lizardbeans/sdvxminicon/img/024.jpg

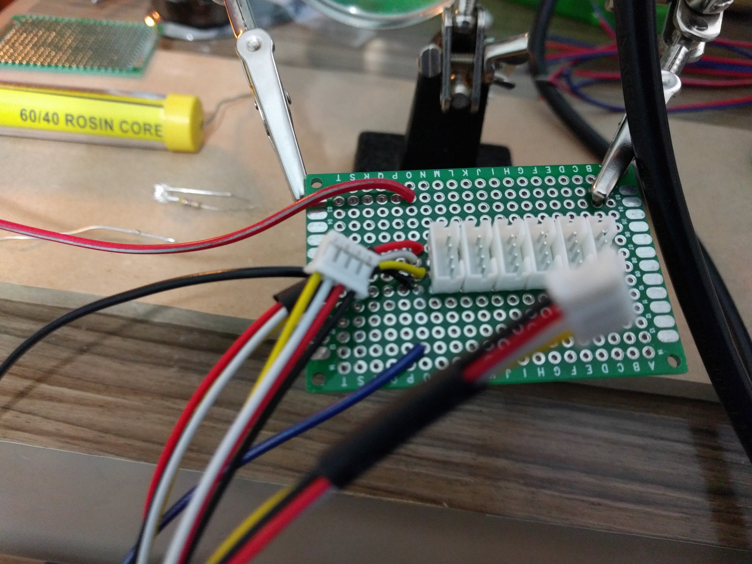
img/024.jpg
