lizardbeans/sdvxminicon/img/025.jpg

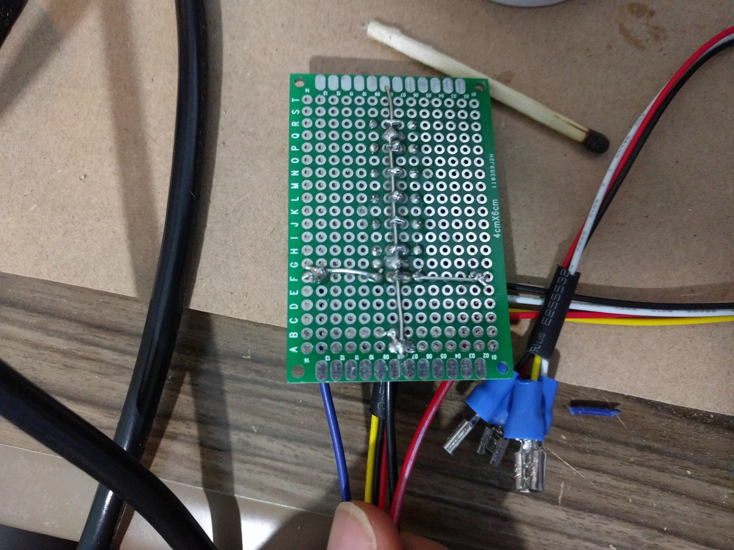
img/025.jpg
