lizardbeans/sdvxminicon/img/026.jpg

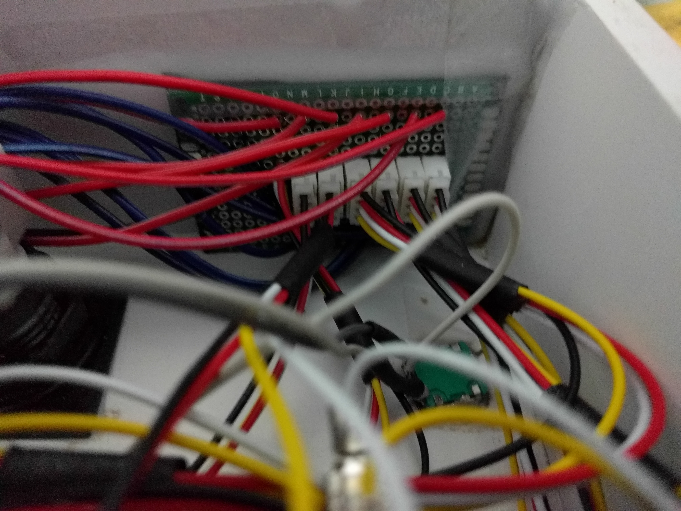
img/026.jpg
