lizardbeans/sdvxminicon/img/028.jpg

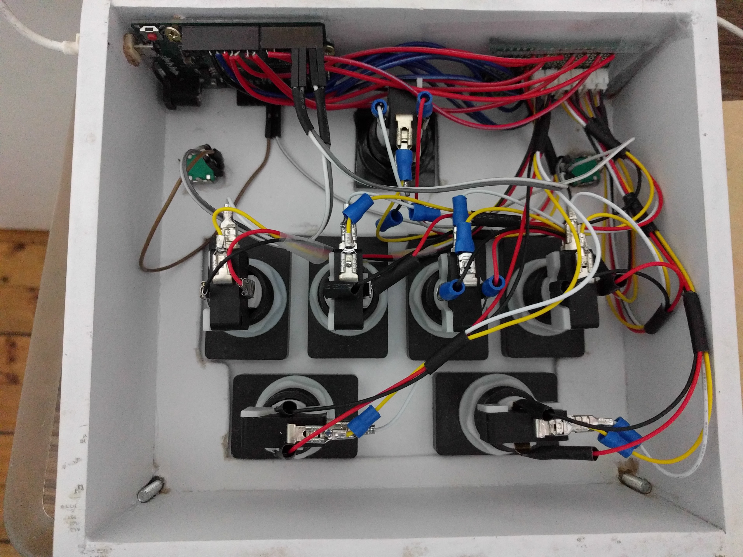
img/028.jpg
